PubInv/moonrat/RiceMiniCubator/CAD_MinicubatorTeam_Cycle5/CADRenderings_MinicubatorTeam_Cycle5.pdf

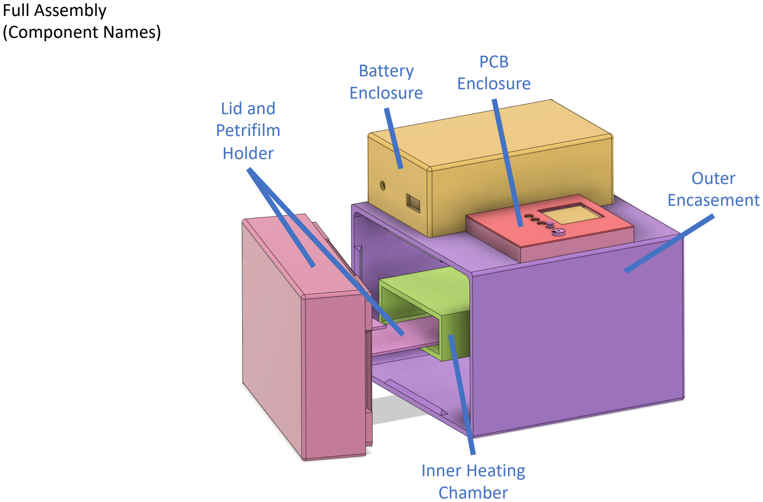
[picture p18: page 1]

Lid and
Petrifilm
Holder
Outer
Encasement

Inner Heating
Chamber

Battery
Enclosure

PCB
Enclosure

Full Assembly
(Component Names)

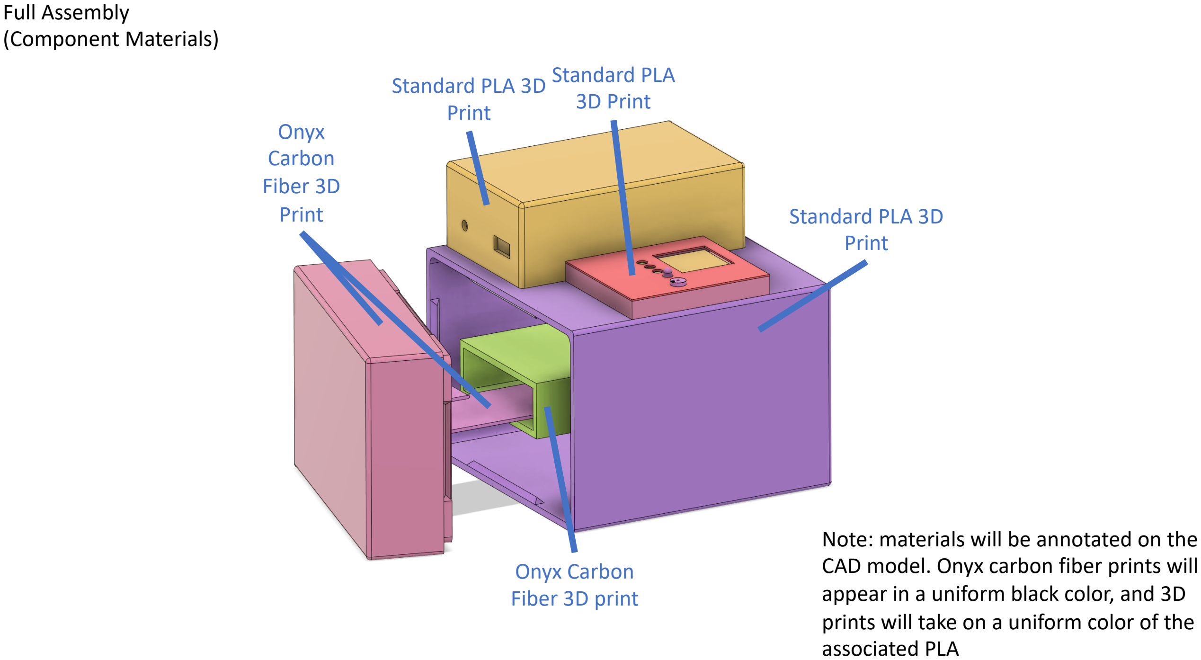
[picture p19: page 2]

Onyx
Carbon
Fiber 3D
Print | Standard PLA 3D
| Print

Onyx Carbon
Fiber 3D print

Standard PLA 3D
Print

Standard PLA
3D Print

Full Assembly
(Component Materials)

Note: materials will be annotated on the CAD model. Onyx carbon fiber prints will appear in a uniform black color, and 3D prints will take on a uniform color of the associated PLA

Inner Heating Chamber
(Material: Onyx Carbon Fiber) Note: this will be represented by a green box in future slides.

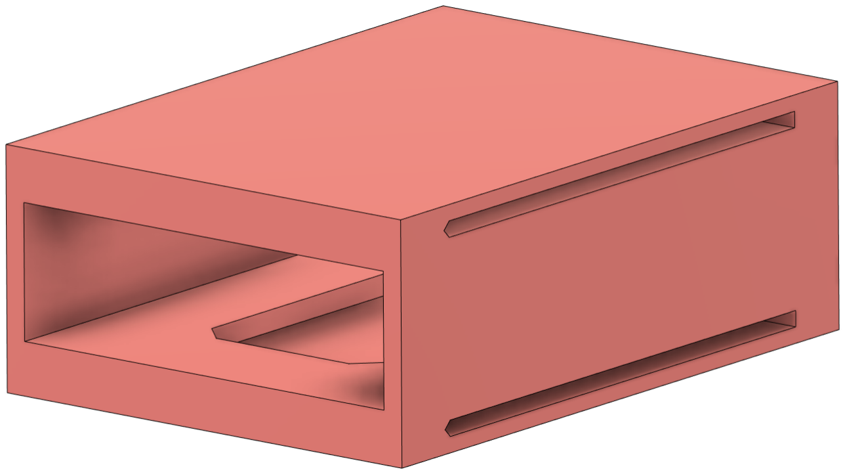
[picture p20: figure]

Inner Heating Chamber +
Outer Encasement, sans
Insulation (Materials
Shown)

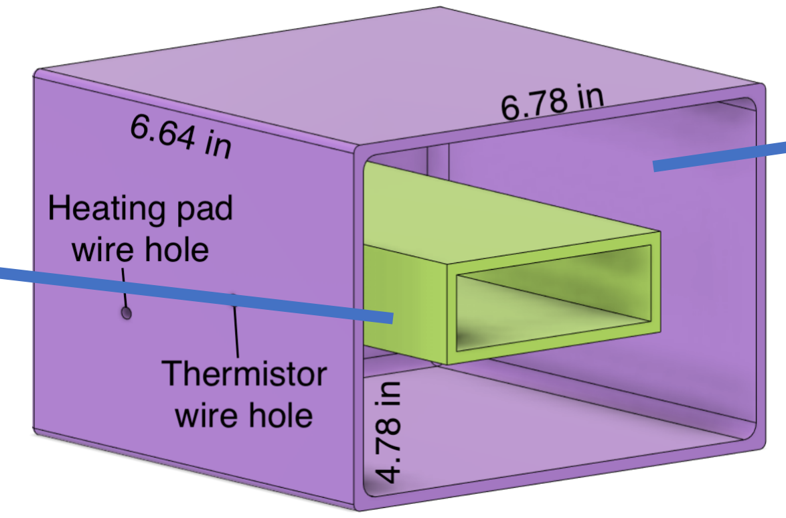
[picture p21: figure]

Onyx Carbon
Fiber

Standard PLA
3D Print

Note: the green inner heating chamber is a representation of the inner heating chamber on the previous slide. The inner dimensions with the petrifilm holder are left unchanged.

Placement of peg
mounting inner heating
chamber to the outer
enclosure

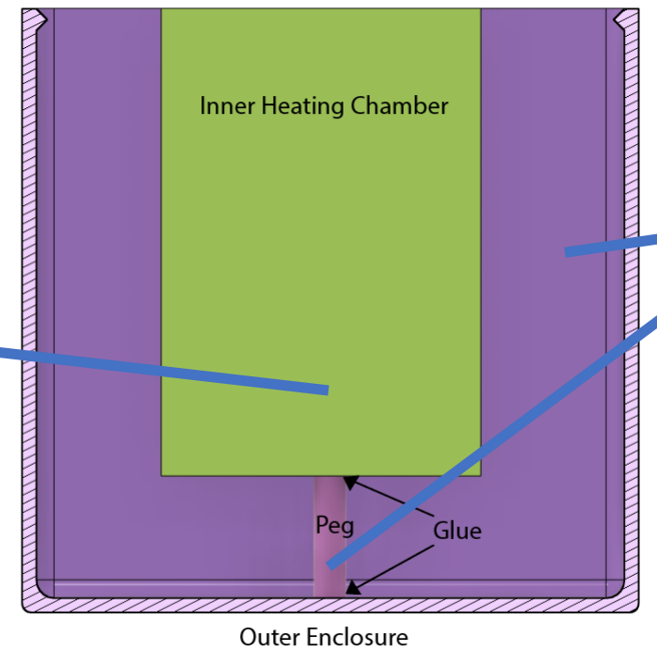
[picture p22: figure]

Onyx Carbon
Fiber

Standard PLA
3D Print

Inner Heating Chamber +
Insulation Material +
Outer Encasement
(Materials Shown)

Standard PLA
3D Print

Expanding

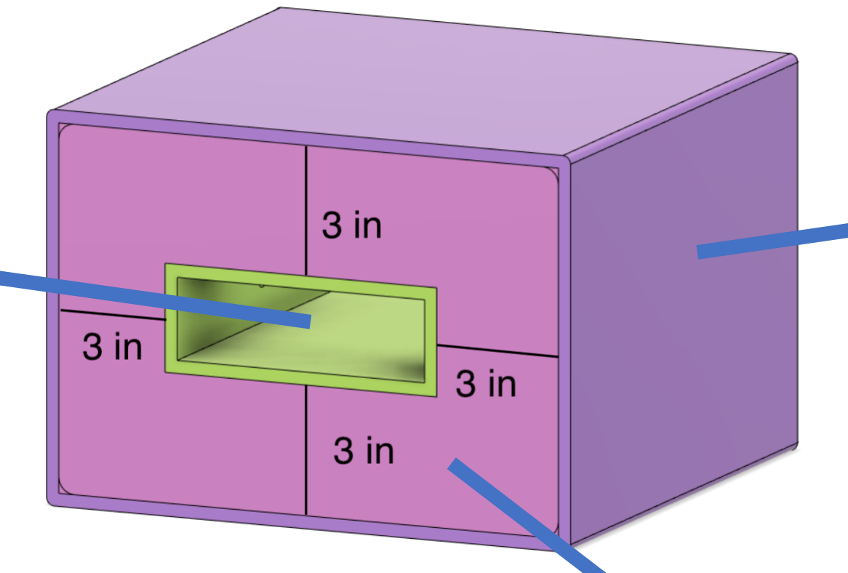
[picture p23: figure]

Polyurethane
Foam

Onyx Carbon
Fiber

Lid + Petrifilm Holder,
sans Insulation (Material: Onyx Carbon Fiber)

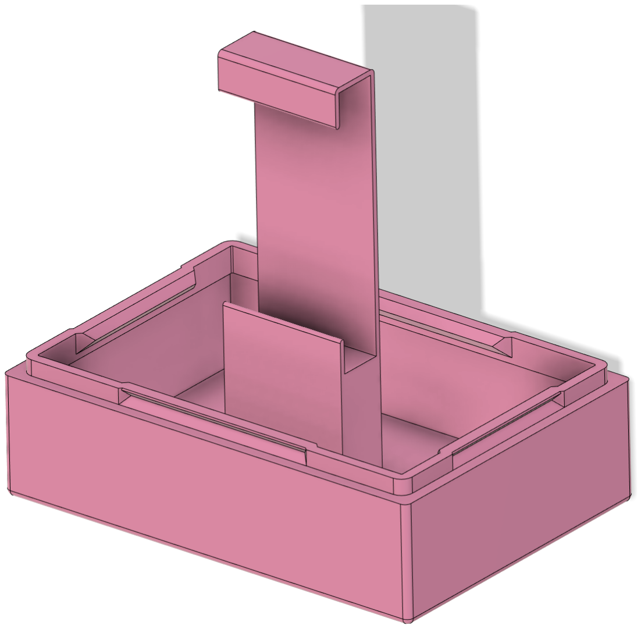
[picture p24: figure]

Lid + Petrifilm Holder,
interfaced with inner
heating chamber and
outer enclosure
(Materials Shown)

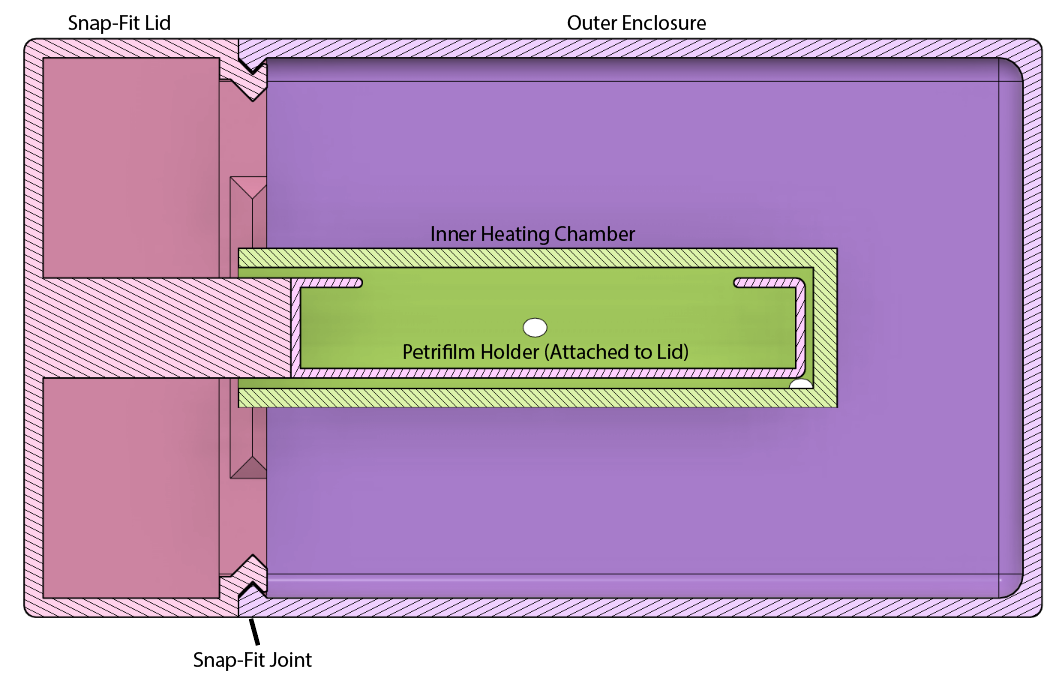
[picture p25: figure]

Onyx Carbon
Fiber
(Magenta,
Green)

PLA (purple)

Battery Enclosure and its mount on the outer encasement
(Material: PLA)

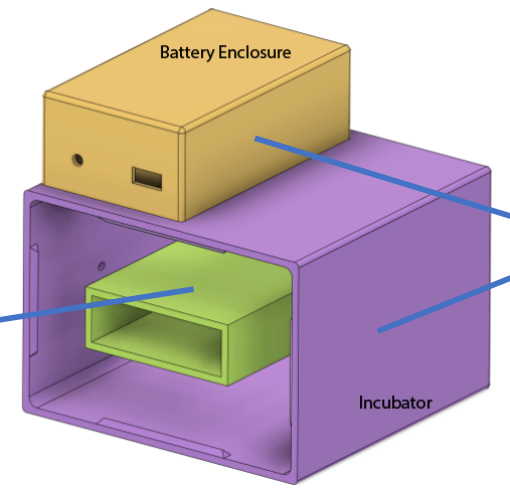
[picture p26: figure]

PLA

Onyx
Carbon
Fiber

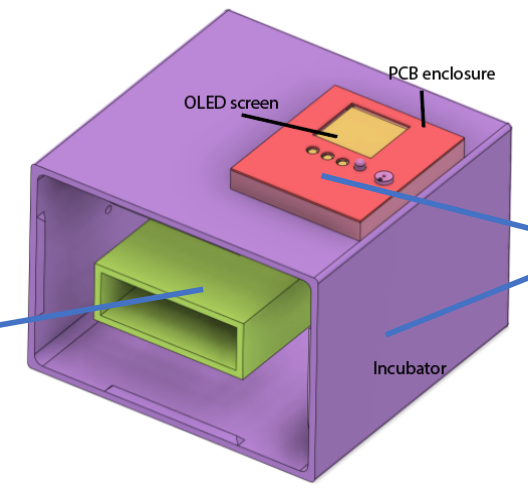
[picture p27: figure]

Onyx
Carbon
Fiber

PLA

PCB Enclosure and its mount on the outer encasement (Material: PLA)
