PubInv/moonrat/moonrat/ArduinoShieldIntermediate/ArduionShieldIntermediateDesign.jpg

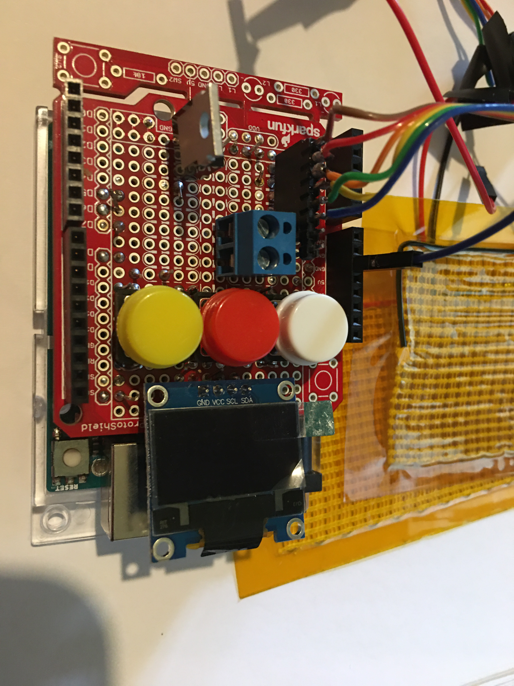
moonrat/ArduinoShieldIntermediate/ArduionShieldIntermediateDesign.jpg
