PubInv/moonrat/moonrat/PCB.gif

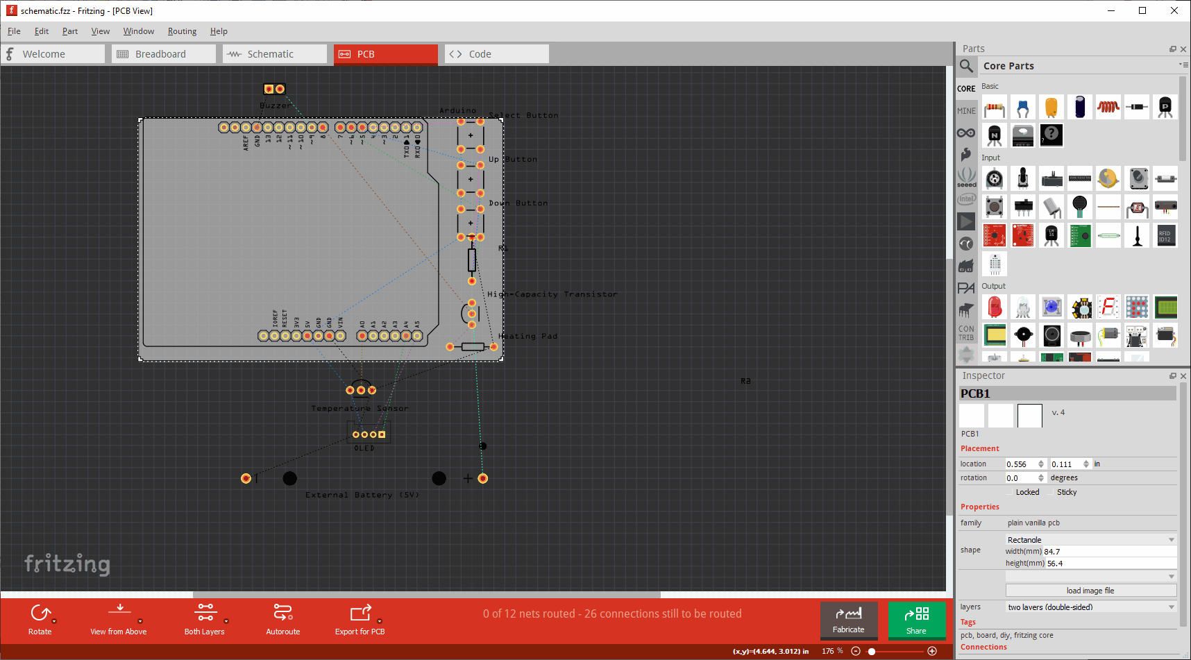
moonrat/PCB.gif
