PubInv/moonrat/moonrat/schematic.gif

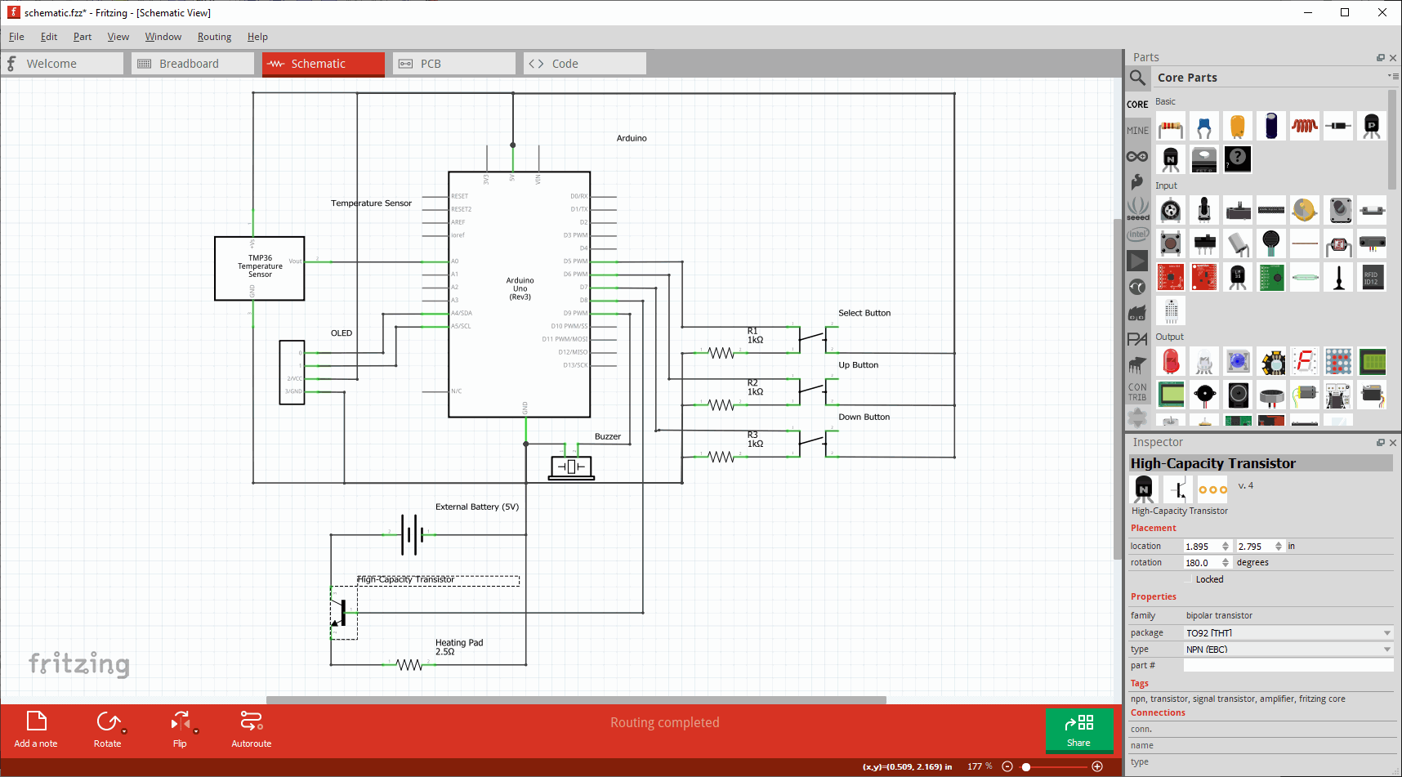
moonrat/schematic.gif
