PubInv/moonrat/moonrat/schematic.jpg

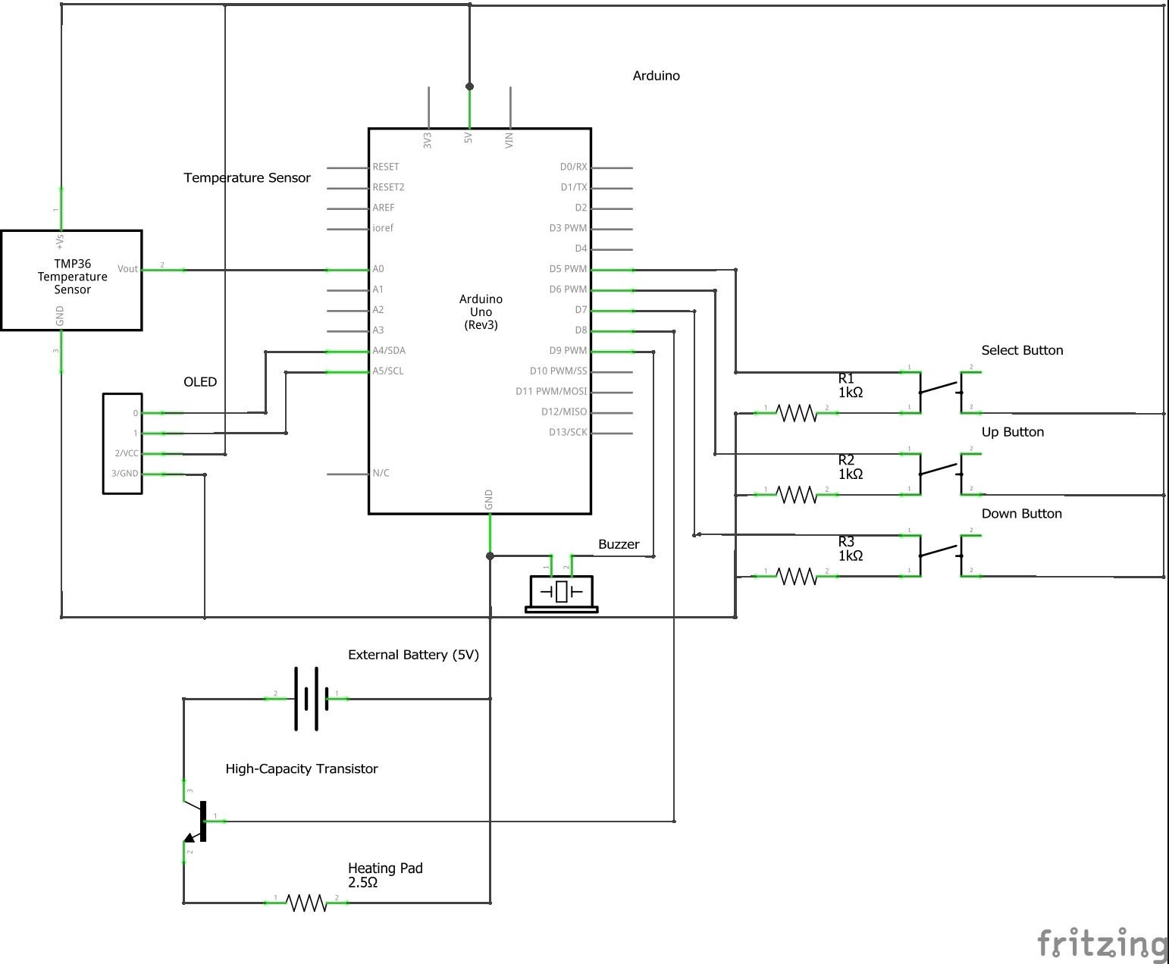
moonrat/schematic.jpg
