PubInv/moonrat/Pictures/IMG-2394.JPG

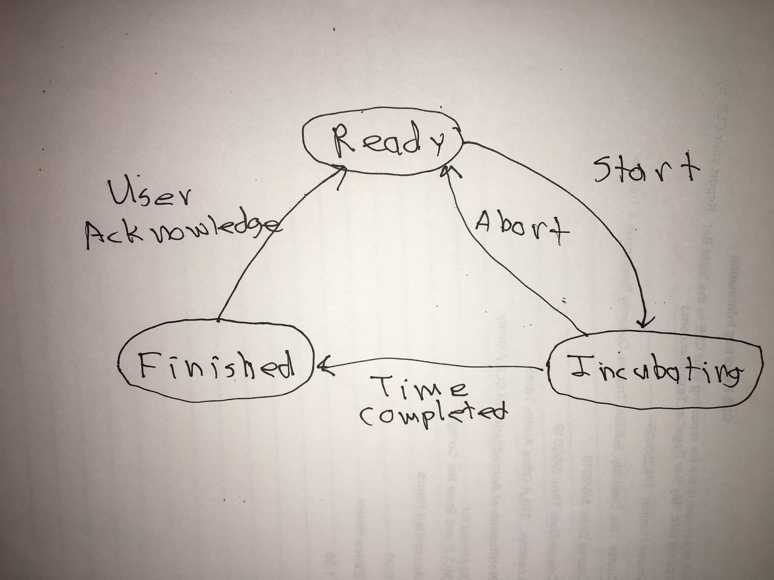
Pictures/IMG-2394.JPG
