PubInv/moonrat/Pictures/September2020/Full_Device.jpg

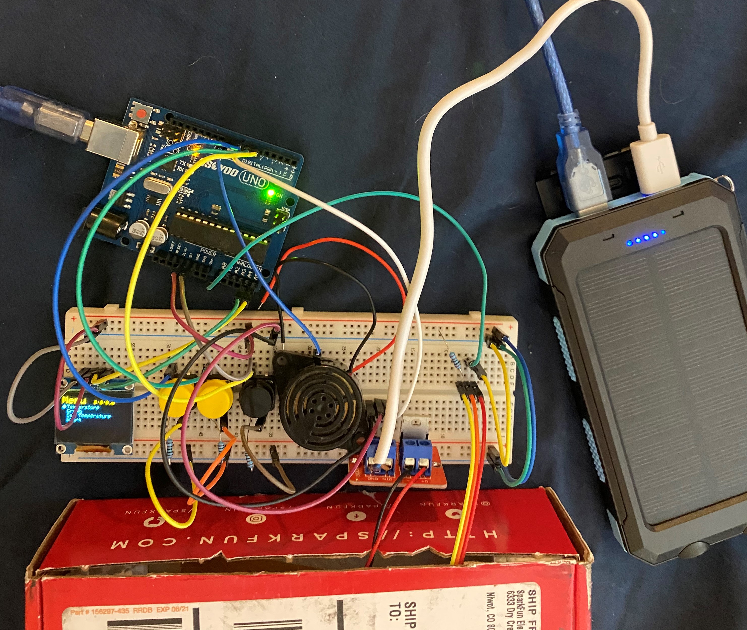
Pictures/September2020/Full_Device.jpg
