PubInv/moonrat/Pictures/September2020/Menu_Focus_2.jpg

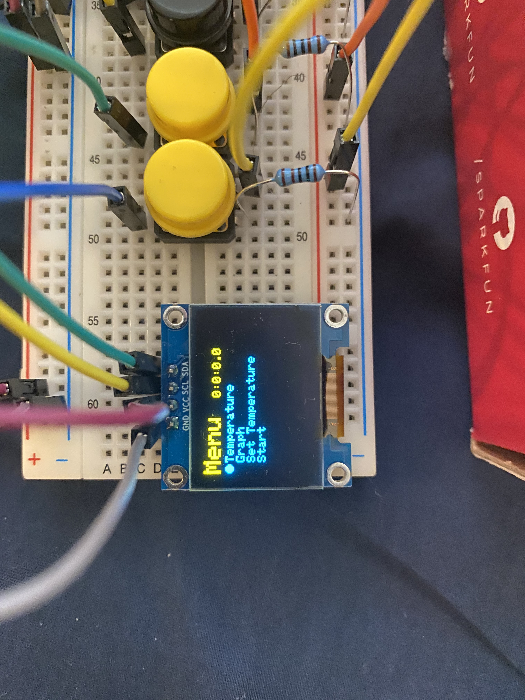
Pictures/September2020/Menu_Focus_2.jpg
