PubInv/moonrat/moonratII/hardware_moonratII/pcb_controller_moonratII/parts/Opossum_2978135/README.txt

Opossum by Amnson on Thingiverse: https://www.thingiverse.com/thing:2978135
