PubInv/moonrat/moonratII/hardware_moonratII/pcb_controller_moonratII/parts/Cable2x5.png

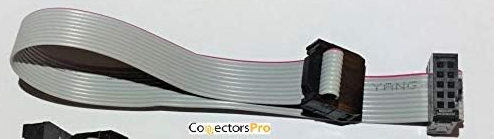
moonratII/hardware_moonratII/pcb_controller_moonratII/parts/Cable2x5.png
