PubInv/moonrat/moonratII/hardware_moonratII/pcb_controller_moonratII/parts/Cable_FemaleGND_2x3.png

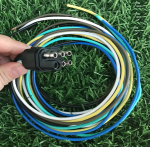
moonratII/hardware_moonratII/pcb_controller_moonratII/parts/Cable_FemaleGND_2x3.png
