PubInv/moonrat/moonratII/hardware_moonratII/pcb_controller_moonratII/parts/U602602_Dimension_New.jpg

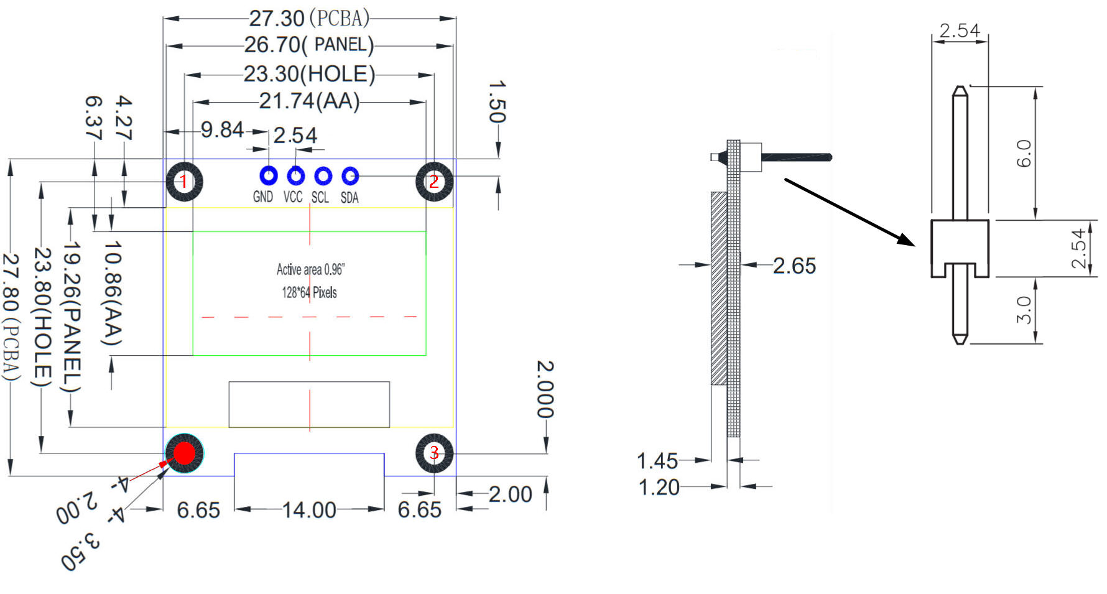
moonratII/hardware_moonratII/pcb_controller_moonratII/parts/U602602_Dimension_New.jpg
