PubInv/moonrat/moonratII/hardware_moonratII/pcb_controller_moonratII/parts/Omron/B3F-6050--3DModel-STEP-273799.STEP

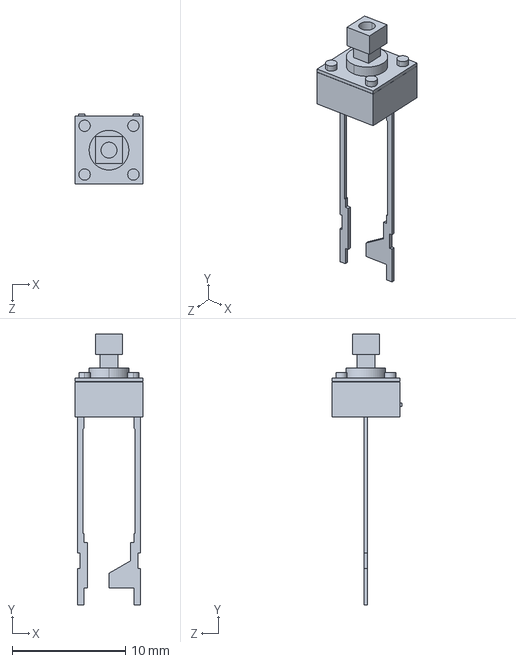
[picture p59: CAD file, 2023-07-31]
moonratII/hardware_moonratII/pcb_controller_moonratII/parts/Omron/B3F-6050--3DModel-STEP-273799.STEP
6.00 x 23.9 x 6.20 mm
