PubInv/moonrat/moonratII/hardware_moonratII/pcb_heaterboard_1_moonratII/parts/KF128 2.54mm/KF128-2.54-12P.step

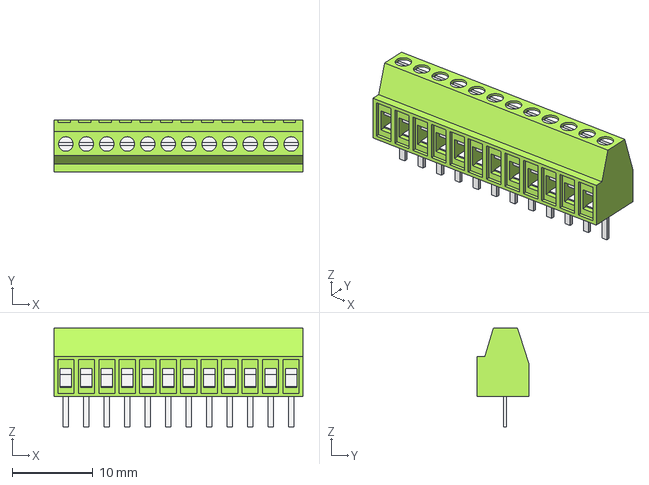
[picture p60: CAD file, 2025-05-26]
moonratII/hardware_moonratII/pcb_heaterboard_1_moonratII/parts/KF128 2.54mm/KF128-2.54-12P.step
30.9 x 6.50 x 12.3 mm
Housing
PlasticBody
