PubInv/moonrat/moonratII/hardware_moonratII/pcb_heaterboard_1_moonratII/parts/SMDRoundNut-PartBody_SMD_RoundNutM2x4x5x1.5.step

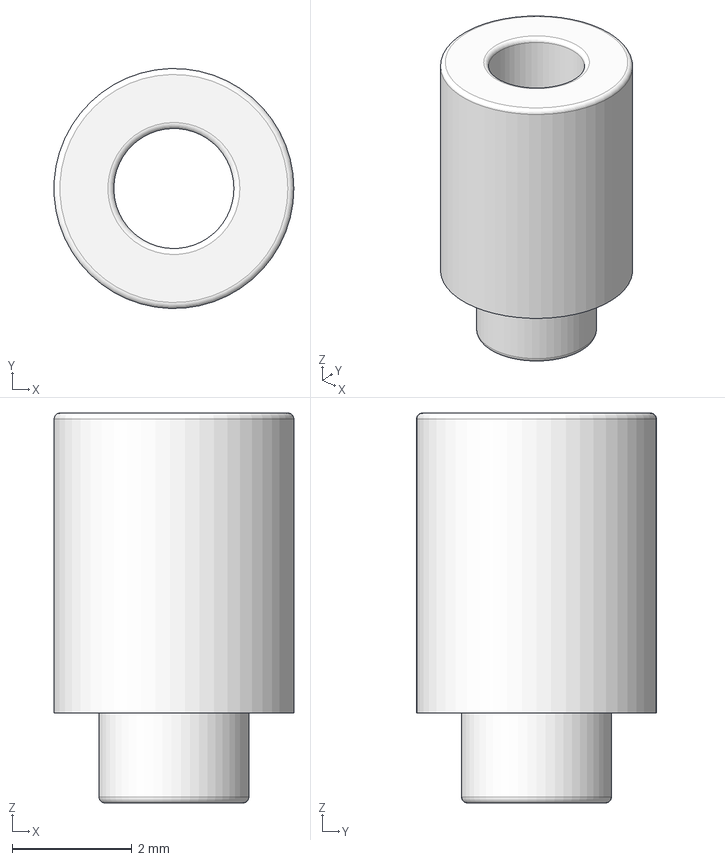
[picture p61: CAD file, 2023-11-20]
moonratII/hardware_moonratII/pcb_heaterboard_1_moonratII/parts/SMDRoundNut-PartBody_SMD_RoundNutM2x4x5x1.5.step
4.00 x 4.00 x 6.50 mm
