PubInv/moonrat/moonratII/hardware_moonratII/pcb_heaterboard_1_moonratII/parts/KF128 2.54mm/KF128-2.54-8P.step

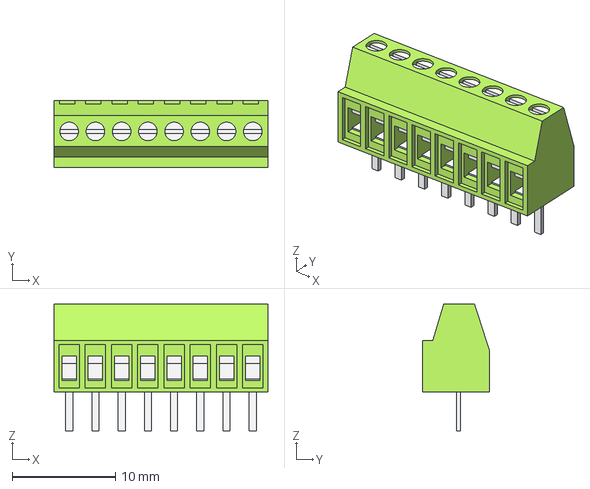
[picture p63: CAD file, 2025-05-26]
moonratII/hardware_moonratII/pcb_heaterboard_1_moonratII/parts/KF128 2.54mm/KF128-2.54-8P.step
20.7 x 6.50 x 12.3 mm
Housing
PlasticBody
