PubInv/moonrat/moonratII/hardware_moonratII/pcb_controller_moonratII/parts/homemade_2mmx3mmx3mmSpacer.FCStd

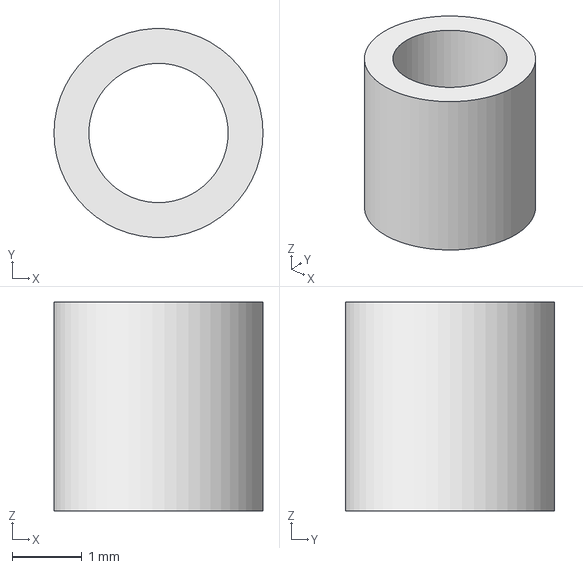
[picture p64: CAD file, 2023-11-19]
moonratII/hardware_moonratII/pcb_controller_moonratII/parts/homemade_2mmx3mmx3mmSpacer.FCStd
3.00 x 2.99 x 3.00 mm
