PubInv/moonrat/moonratII/hardware_moonratII/pcb_heaterboard_1_moonratII/parts/KF128 2.54mm/KF128-2.54-5P.step

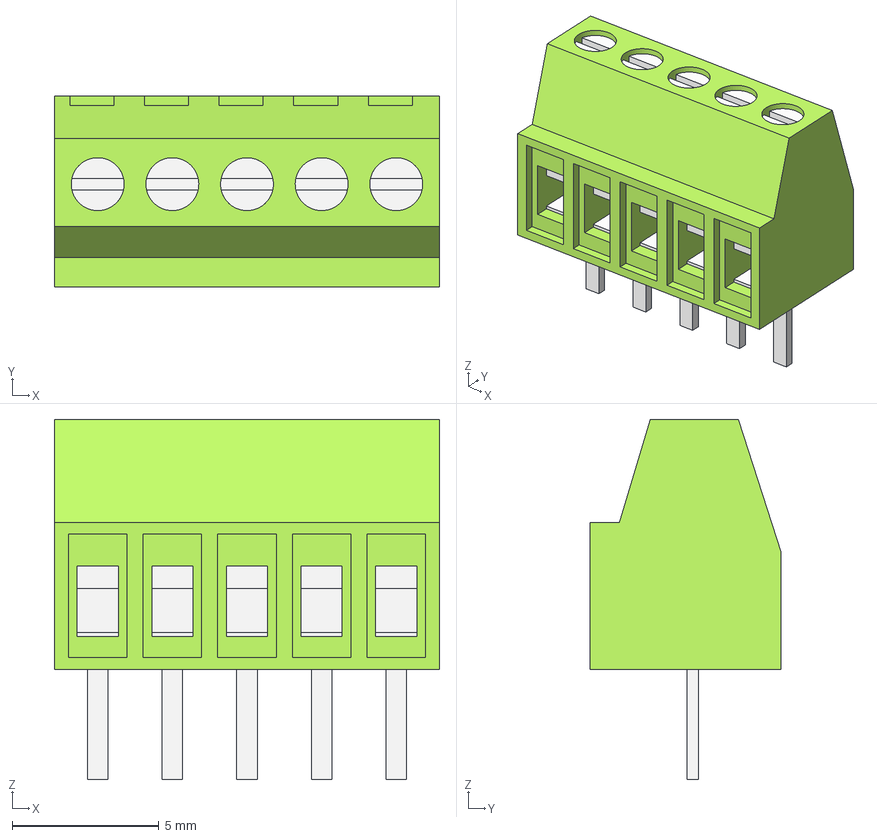
[picture p65: CAD file, 2025-05-26]
moonratII/hardware_moonratII/pcb_heaterboard_1_moonratII/parts/KF128 2.54mm/KF128-2.54-5P.step
13.1 x 6.50 x 12.3 mm
Housing
PlasticBody
