PubInv/moonrat/moonratII/hardware_moonratII/pcb_heaterboard_1_moonratII/parts/Pantalla OLED 0.96'' 128x64.stp

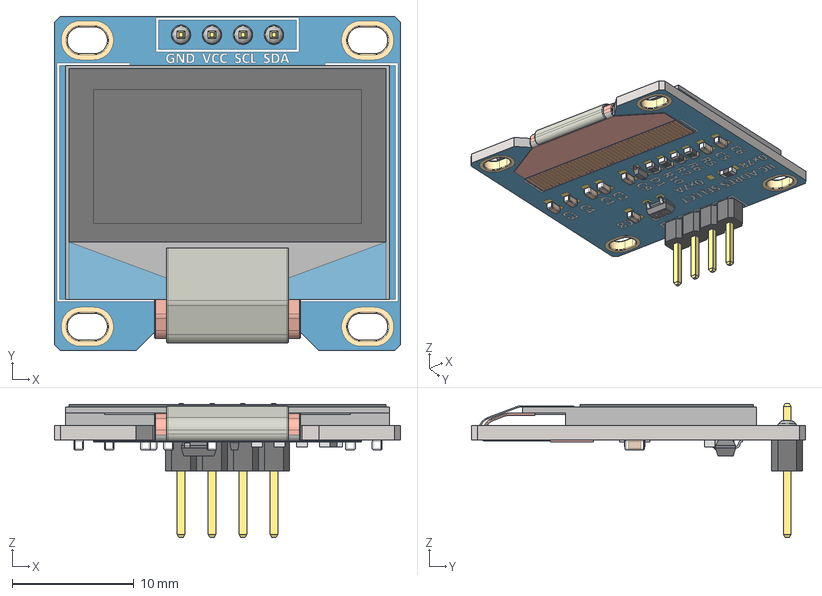
[picture p66: CAD file, 2023-11-19]
moonratII/hardware_moonratII/pcb_heaterboard_1_moonratII/parts/Pantalla OLED 0.96'' 128x64.stp
28.4 x 27.4 x 11.0 mm
SOT-23_TOR
RES_CR16_MTK_1 x 4
RES_CR16_MTK
SOD323F_DIO
