PubInv/moonrat/moonratII/hardware_moonratII/pcb_heaterboard_1_moonratII/parts/KF128 2.54mm/KF128-2.54-11P.step

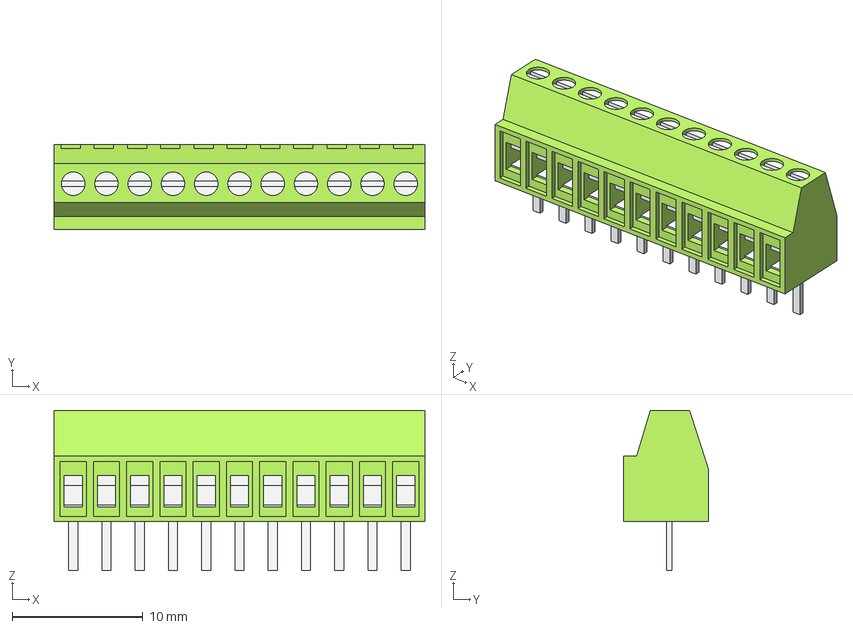
[picture p67: CAD file, 2025-05-26]
moonratII/hardware_moonratII/pcb_heaterboard_1_moonratII/parts/KF128 2.54mm/KF128-2.54-11P.step
28.3 x 6.50 x 12.3 mm
Housing
PlasticBody
