PubInv/moonrat/moonratII/hardware_moonratII/pcb_controller_moonratII/parts/SSD1306_OLED_Display(128x64).step

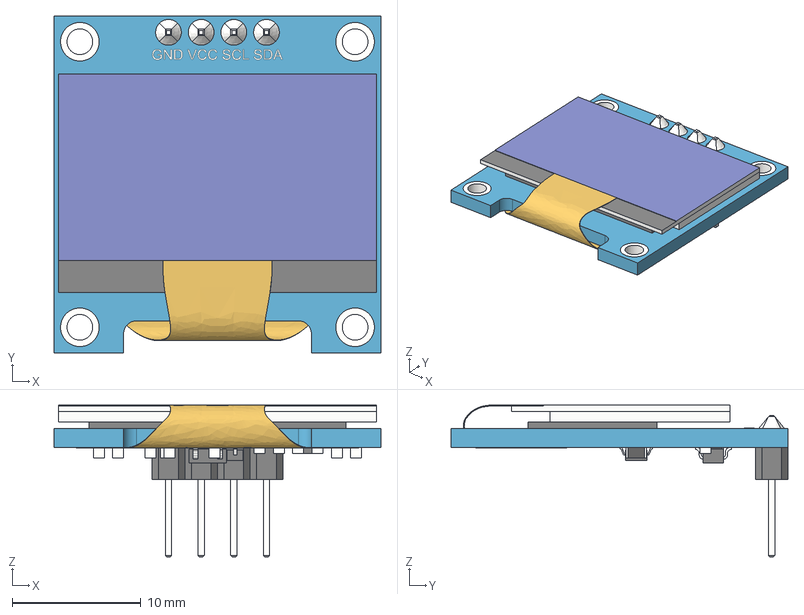
[picture p69: CAD file, 2023-08-16]
moonratII/hardware_moonratII/pcb_controller_moonratII/parts/SSD1306_OLED_Display(128x64).step
25.4 x 26.2 x 11.8 mm
board
screen
pin_header
soldering
smd_capacitor
smd_capacitor (1)
914_smd_resistor
472_smd_resistor x 3
t4_smd_diode
smd_capacitor (2)
smd_capacitor (3)
smd_capacitor (4)
smd_capacitor (5)
smd_capacitor (6)
472_smd_resistor (1)
SOT-23_XC6206 v3
smd_capacitor (7)
flat_cable
