PubInv/moonrat/moonratII/hardware_moonratII/pcb_controller_moonratII/parts/BarrelJackSMD v3.step

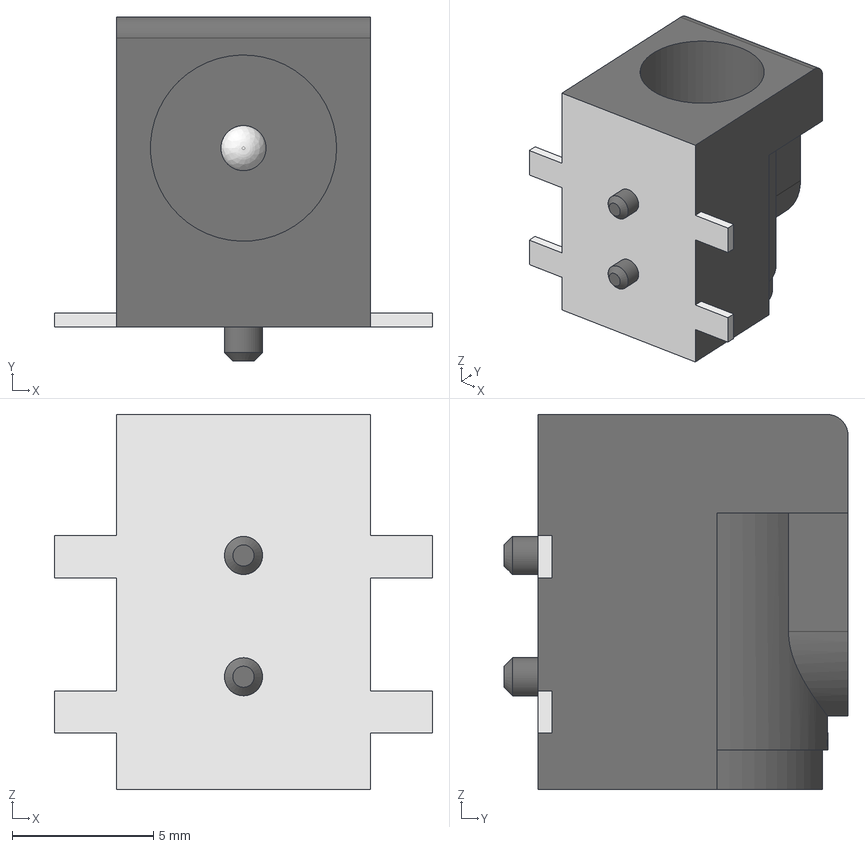
[picture p71: CAD file, 2023-08-03]
moonratII/hardware_moonratII/pcb_controller_moonratII/parts/BarrelJackSMD v3.step
13.4 x 12.2 x 13.3 mm
