PubInv/moonrat/moonratII/hardware_moonratII/pcb_heaterboard_1_moonratII/manufacturing_test/Assembly_photos_Rev1/20240217_200506.jpg

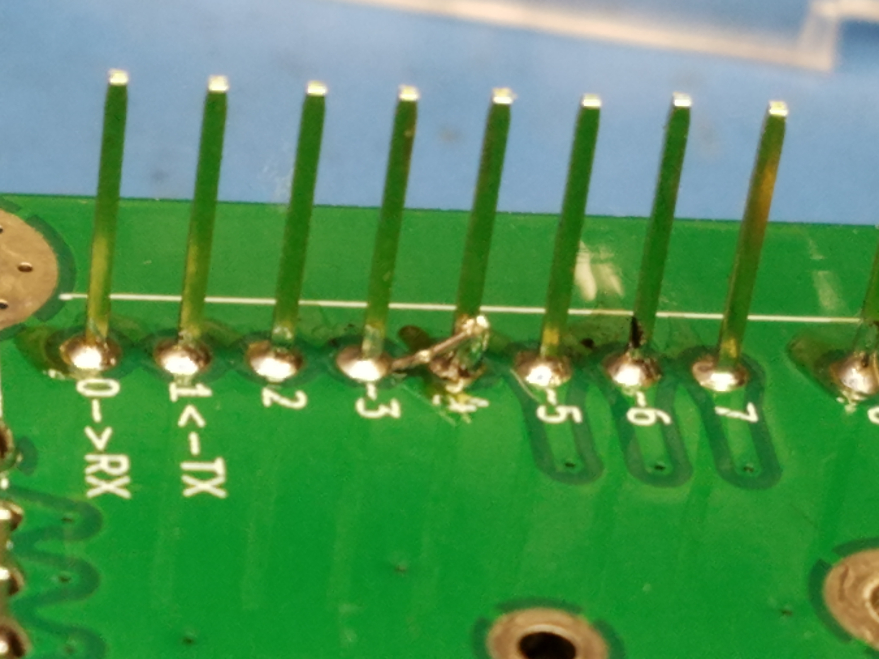
moonratII/hardware_moonratII/pcb_heaterboard_1_moonratII/manufacturing_test/Assembly_photos_Rev1/20240217_200506.jpg
