PubInv/moonrat/moonratII/testing_moonratII/heat_map_moonratII/3d_view.png

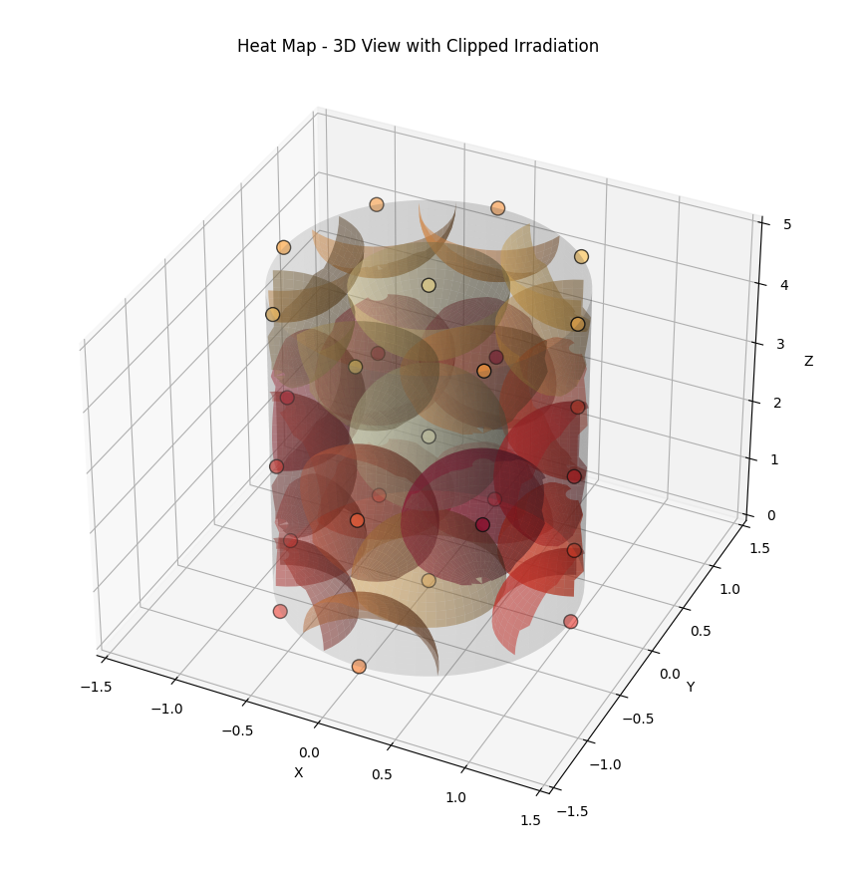
moonratII/testing_moonratII/heat_map_moonratII/3d_view.png
