PubInv/moonrat/moonratII/testing_moonratII/heat_map_moonratII/lat_view.png

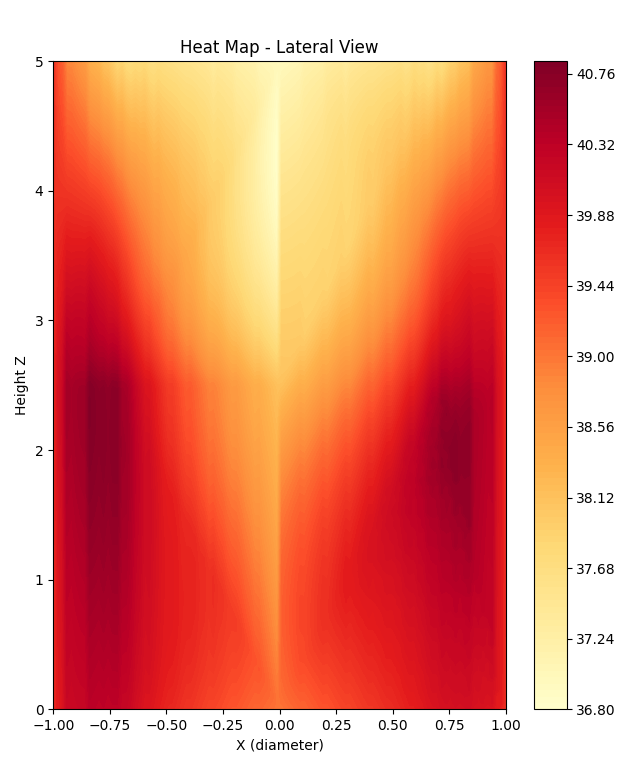
moonratII/testing_moonratII/heat_map_moonratII/lat_view.png
