PubInv/moonrat/moonratII/testing_moonratII/heat_map_moonratII/top_view.png

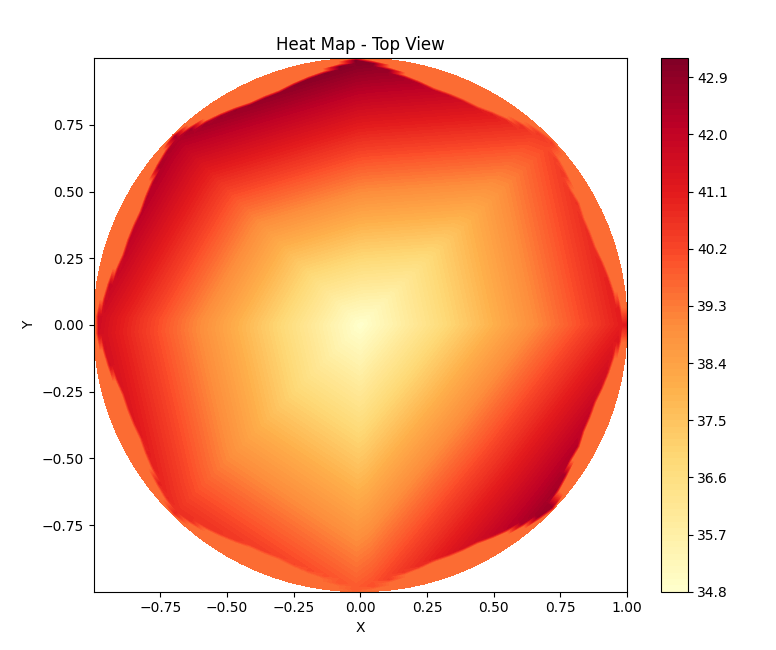
moonratII/testing_moonratII/heat_map_moonratII/top_view.png
