PubInv/moonrat/moonratII/hardware_moonratII/pcb_controller_moonratII/parts/C5665.pdf

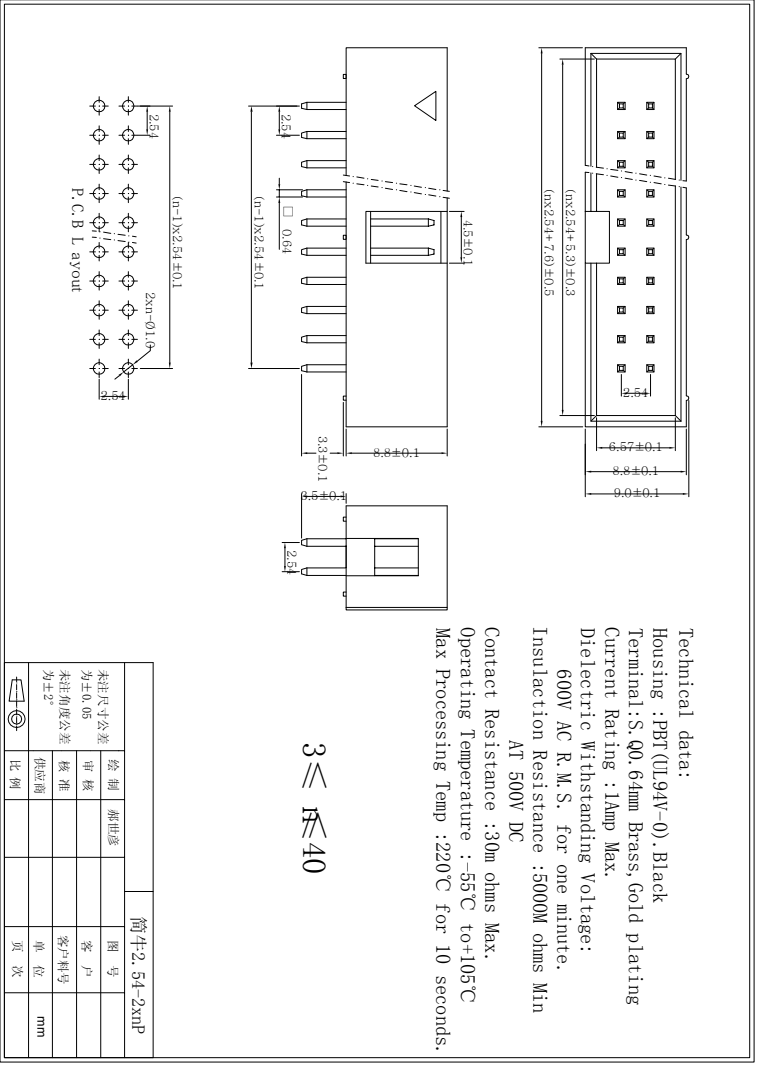
[picture p118: page 1]
P.C.B L ayout; Technical data:; 简牛2.54-2xnP; 未注角度公差; 未注尺寸公差; 供应商; 客户料号; 郝世彦

Max Processing Temp :220℃ for 10 seconds.

Operating Temperature :-55℃ to+105℃

Contact Resistance :30m ohms Max.

Insulaction Resistance :5000M ohms Min

Dielectric Withstanding Voltage:

Current Rating :1Amp Max.

Terminal:S.Q0.64mm Brass,Gold plating

Housing :PBT(UL94V-0).Black

600V AC R.M.S. for one minute.
