PubInv/moonrat/moonratII/hardware_moonratII/pcb_controller_moonratII/parts/DB128V-5.08-2P-GN-S.pdf

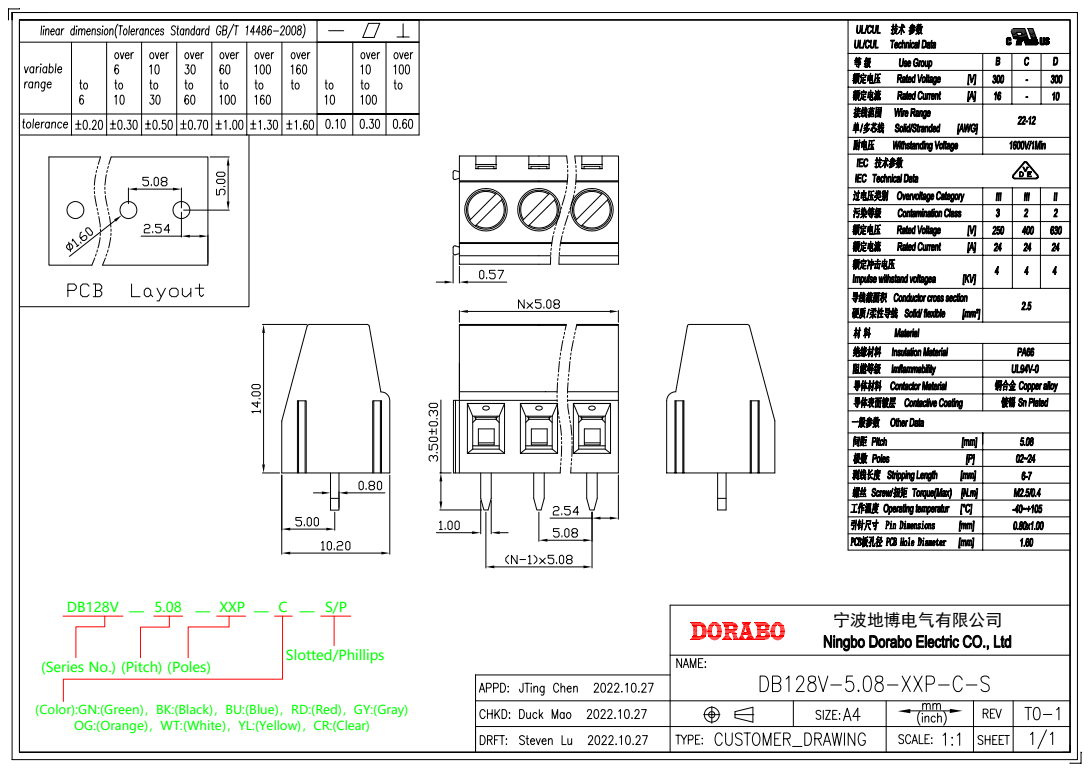
[picture p119: page 1]
— XXP; — S/P (Series No.) (Pitch) (Poles); Slotted/Phillips; 宁波地博电气有限公司 (Color):GN:(Green)，BK:(Black)，BU:(Blue)，RD:(Red)，GY:(Gray) OG:(Orange)，WT:(White)，YL:(Yellow)，CR:(Clear)
