PubInv/moonrat/RiceMiniCubator/MicrocontrollerCode_MinicubatorTeam_Cycle5.pdf

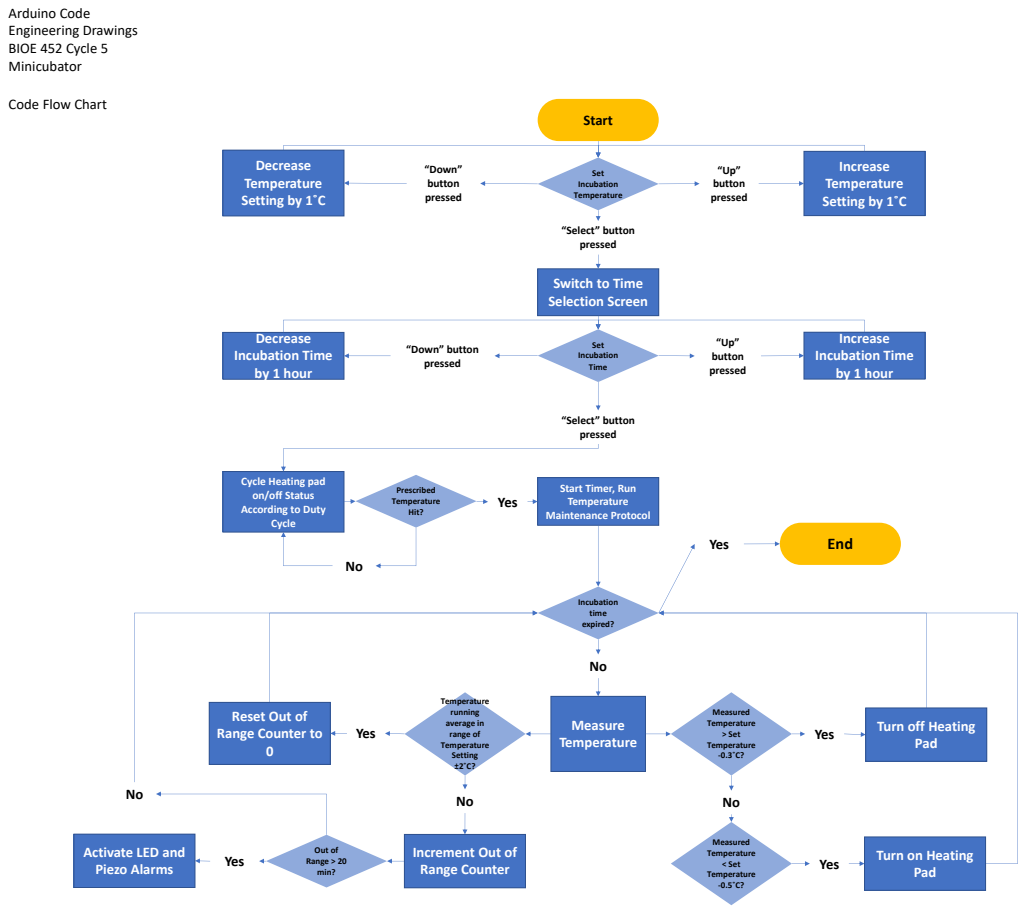
[picture p120: page 1]
Arduino Code Engineering Drawings BIOE 452 Cycle 5 Minicubator; Start; Set Incubation Temperature; Decrease Temperature Setting by 1˚C; Increase Temperature Setting by 1˚C; Set Incubation Time; Decrease Incubation Time by 1 hour; Increase Incubation Time by 1 hour; “Down” button pressed; “Up” button pressed; “Select” button pressed; Incubation time expired?; End; Measured Temperature > Set Temperature -0.3˚C?; Measured Temperature < Set Temperature -0.5˚C?; Yes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

Code Flow Chart

Switch to Time
Selection Screen

Cycle Heating pad
on/off Status
According to Duty
Cycle

Start Timer, Run
Temperature
Maintenance Protocol

Reset Out of
Range Counter to

Turn off Heating
Pad

Activate LED and
Piezo Alarms

Increment Out of
Range Counter

Turn on Heating

## User Control

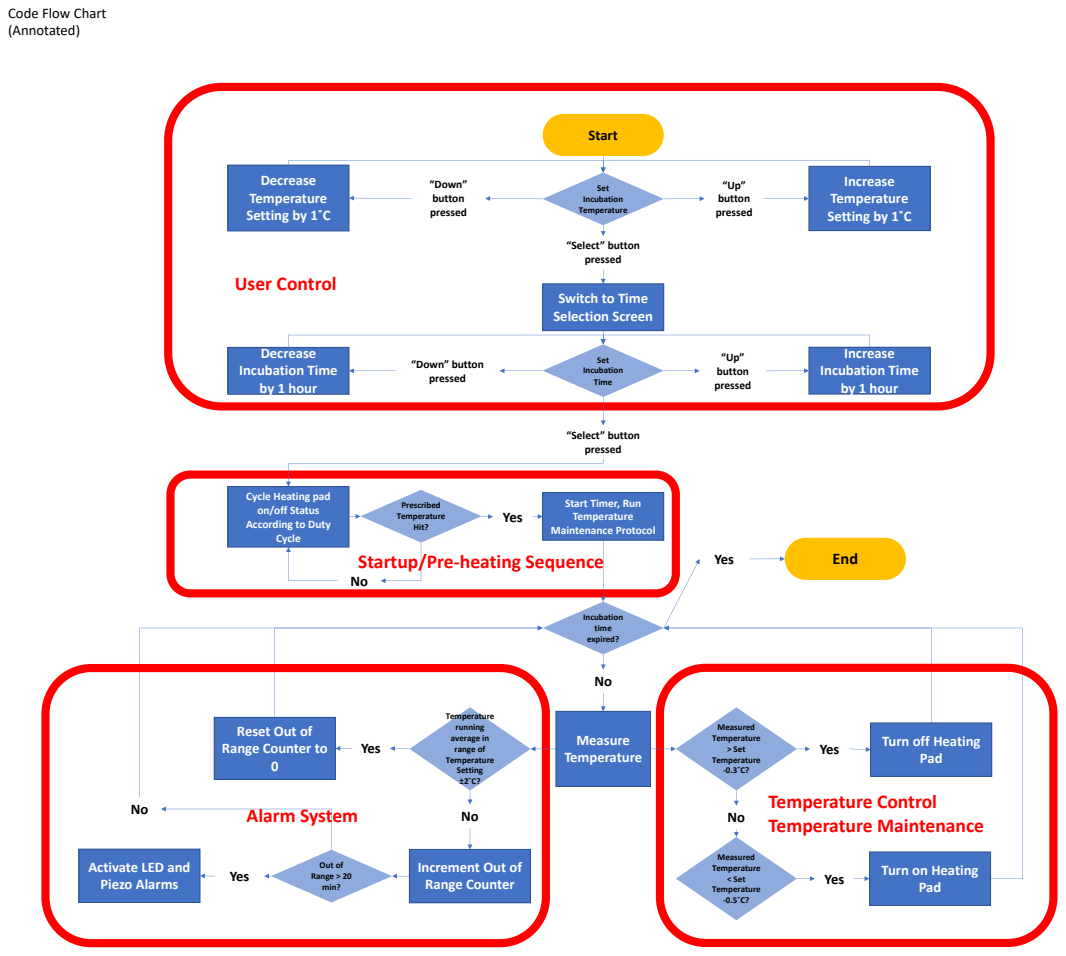
[picture p121: page 2]
Start; Set Incubation Temperature; Decrease Temperature Setting by 1˚C; Increase Temperature Setting by 1˚C; Set Incubation Time; Decrease Incubation Time by 1 hour; Increase Incubation Time by 1 hour; “Down” button pressed; “Up” button pressed; “Select” button pressed; Incubation time expired?; End; Measured Temperature > Set Temperature -0.3˚C?; Measured Temperature < Set Temperature -0.5˚C?; Yes; Temperature running average in range of Temperature Setting ±2˚C?; Out of Range > 20 min?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

Code Flow Chart
(Annotated)

Switch to Time
Selection Screen

Cycle Heating pad
on/off Status
According to Duty
Cycle

Start Timer, Run
Temperature
Maintenance Protocol

Reset Out of
Range Counter to

Turn off Heating
Pad

Activate LED and
Piezo Alarms

Increment Out of
Range Counter

Turn on Heating
