PubInv/moonrat/RiceMiniCubator/CAD_MinicubatorTeam_Cycle5/InnerHeatingChamber_MinicubatorTeam_Cycle5.pdf

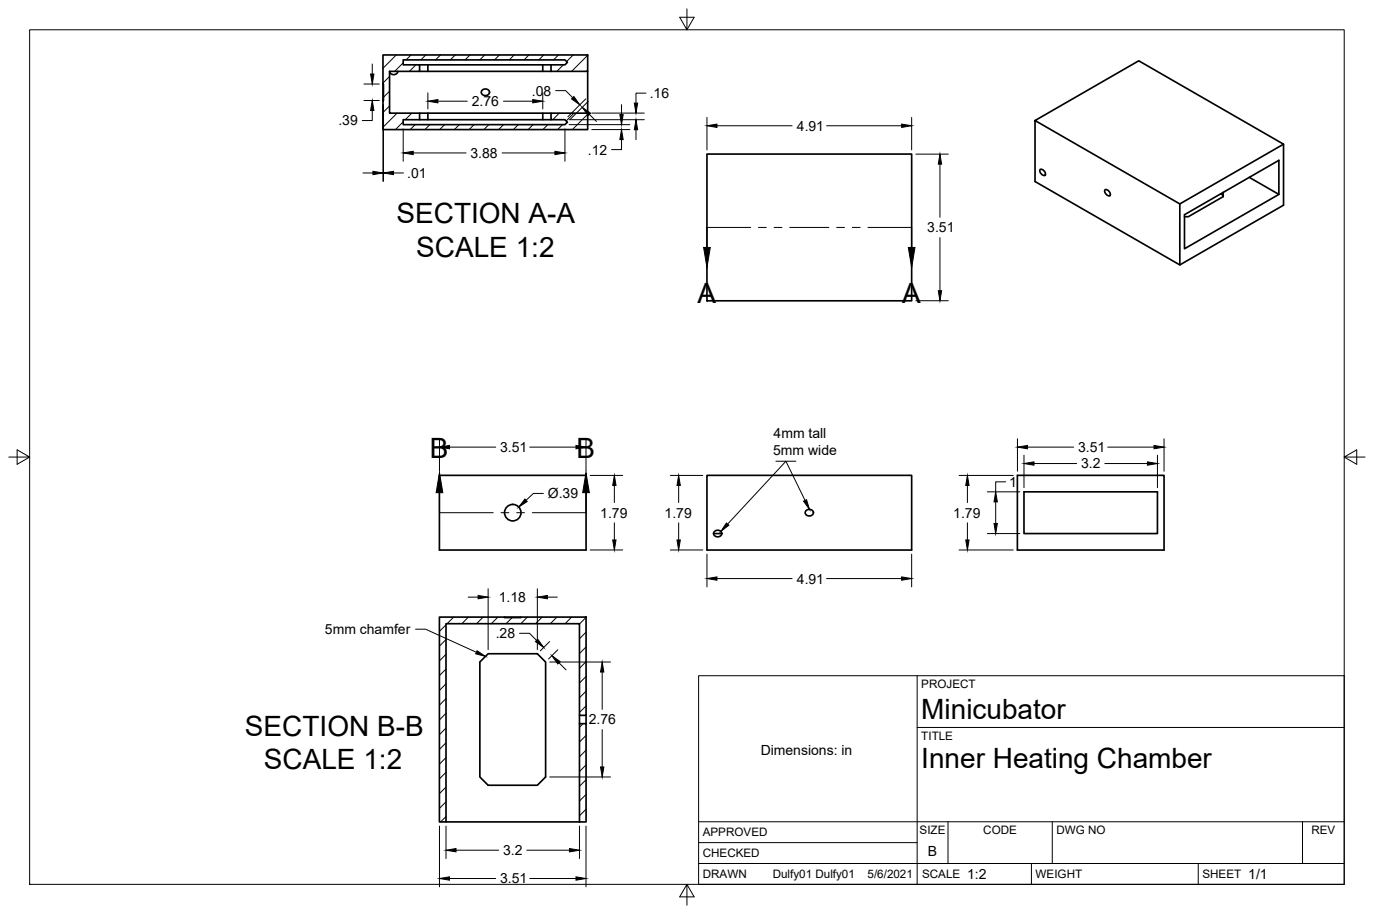
[picture p122: page 1]
SIZE; CODE; DWG NO; REV; Dulfy01 Dulfy01 5/6/2021; 4mm tall 5mm wide; SECTION A-A SCALE 1:2; SECTION B-B SCALE 1:2; .28 5mm chamfer; Dimensions: in

PROJECT
Minicubator
Inner Heating Chamber
