PubInv/moonrat/RiceMiniCubator/CAD_MinicubatorTeam_Cycle5/LidPetrifilmHolder_MinicubatorTeam_Cycle4.pdf

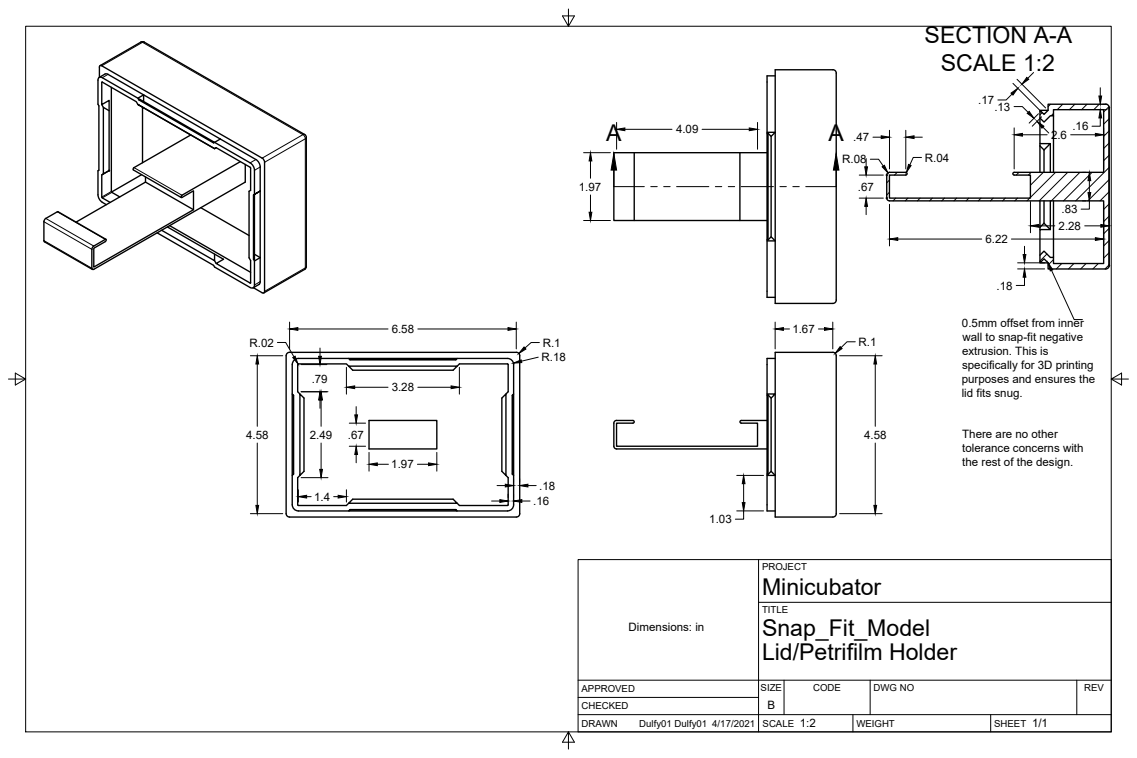
[picture p123: page 1]
SIZE; CODE; DWG NO; REV; Dulfy01 Dulfy01 4/17/2021; Lid/Petrifilm Holder; SECTION A-A SCALE 1:2; Dimensions: in

0.5mm offset from inner
wall to snap-fit negative
extrusion. This is
specifically for 3D printing
purposes and ensures the
lid fits snug.

There are no other
tolerance concerns with
the rest of the design.
