PubInv/moonrat/RiceMiniCubator/CAD_MinicubatorTeam_Cycle5/OuterEncasement_MinicubatorTeam_Cycle4.pdf

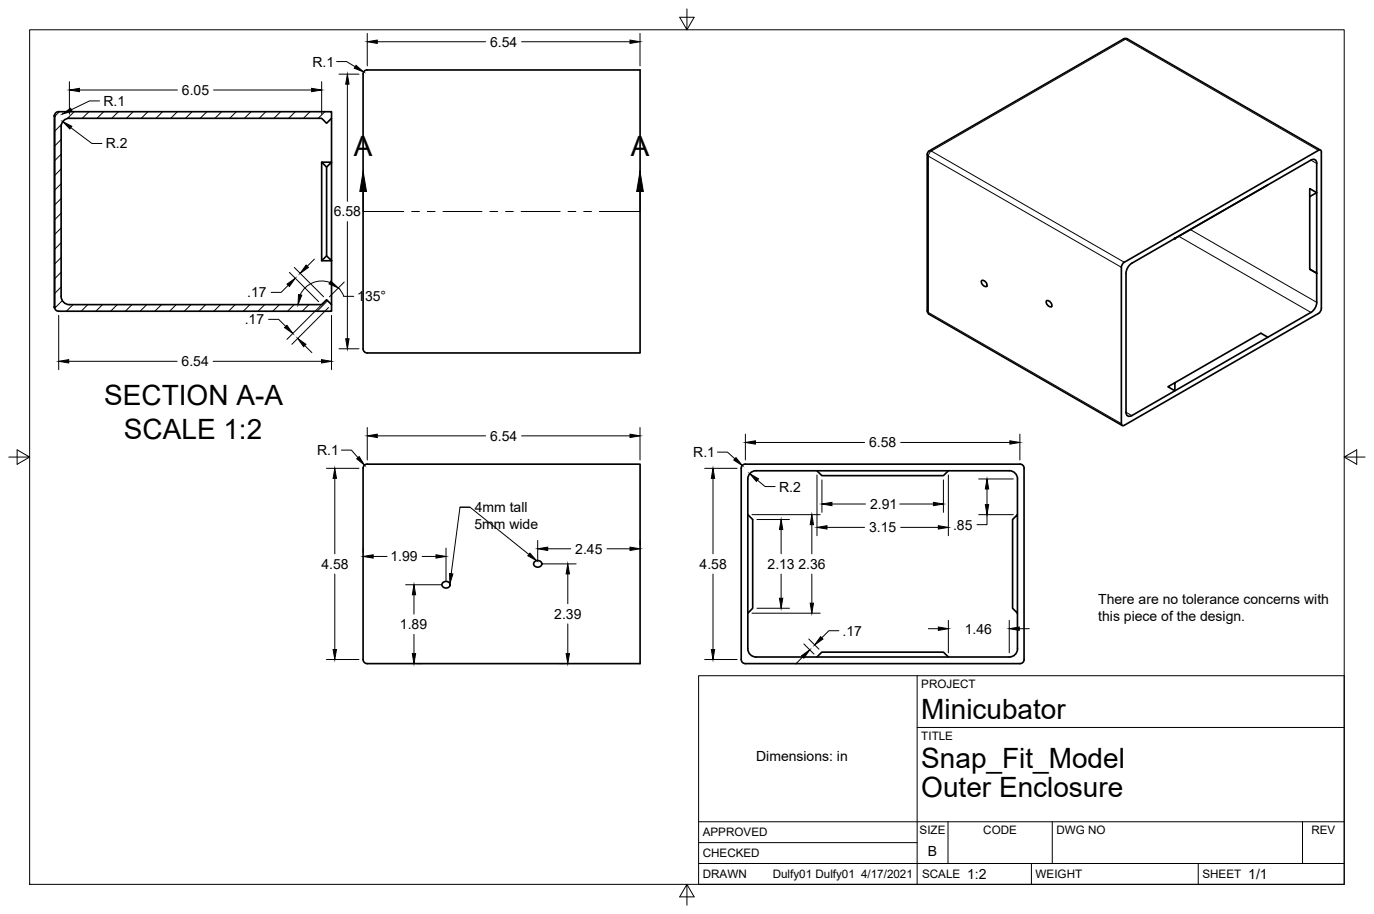
[picture p124: page 1]
SIZE; CODE; DWG NO; REV; Dulfy01 Dulfy01 4/17/2021; Outer Enclosure; SECTION A-A SCALE 1:2; 4mm tall 5mm wide; Dimensions: in

There are no tolerance concerns with
this piece of the design.
