PubInv/moonrat/RiceMiniCubator/CAD_MinicubatorTeam_Cycle5/BatteryEnclosure_MinicubatorTeam_Cycle4.pdf

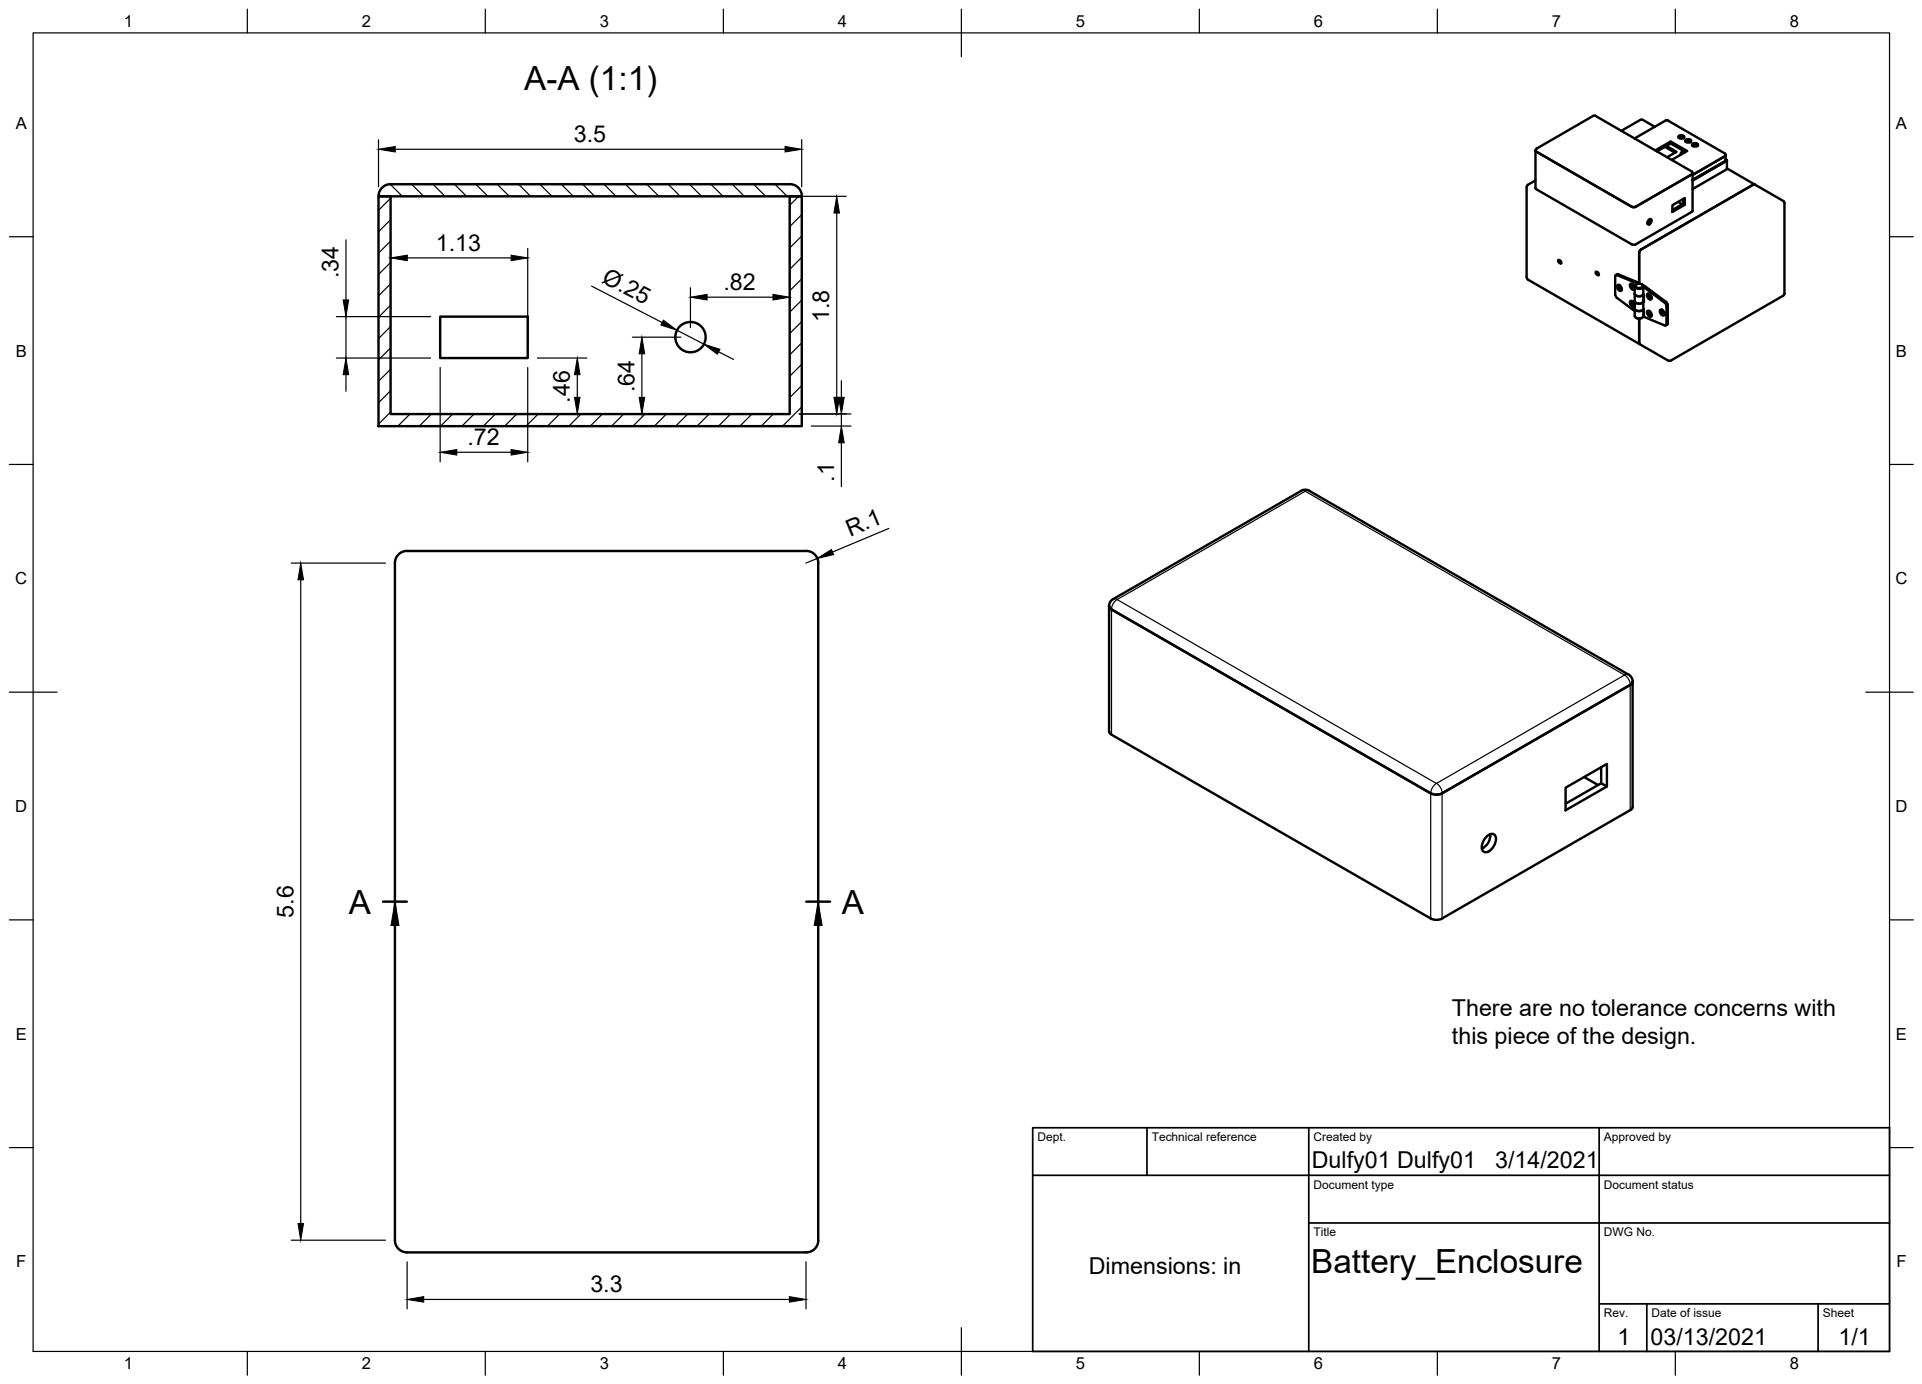
[picture p125: page 1]
Title; DWG No.; Rev.; Date of issue; Sheet; Dimensions: in .64

There are no tolerance concerns with
this piece of the design.

Dept. | Technical reference | Created by Dulfy01 Dulfy01 3/14/2021 | Approved by

Document type | Document status
