PubInv/moonrat/Pictures/September2020/Menu_Focus.jpg

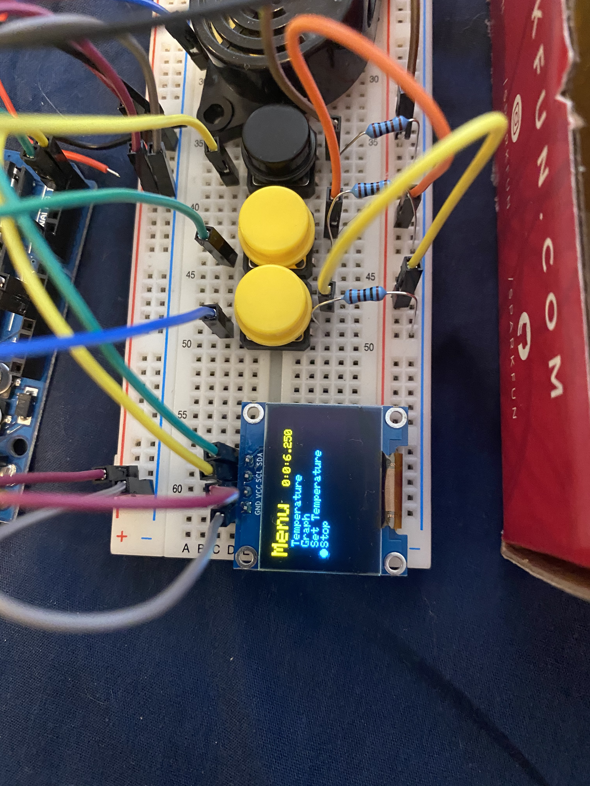
Pictures/September2020/Menu_Focus.jpg
