PubInv/moonrat/Pictures/September2020/Temperature_Reading.jpg

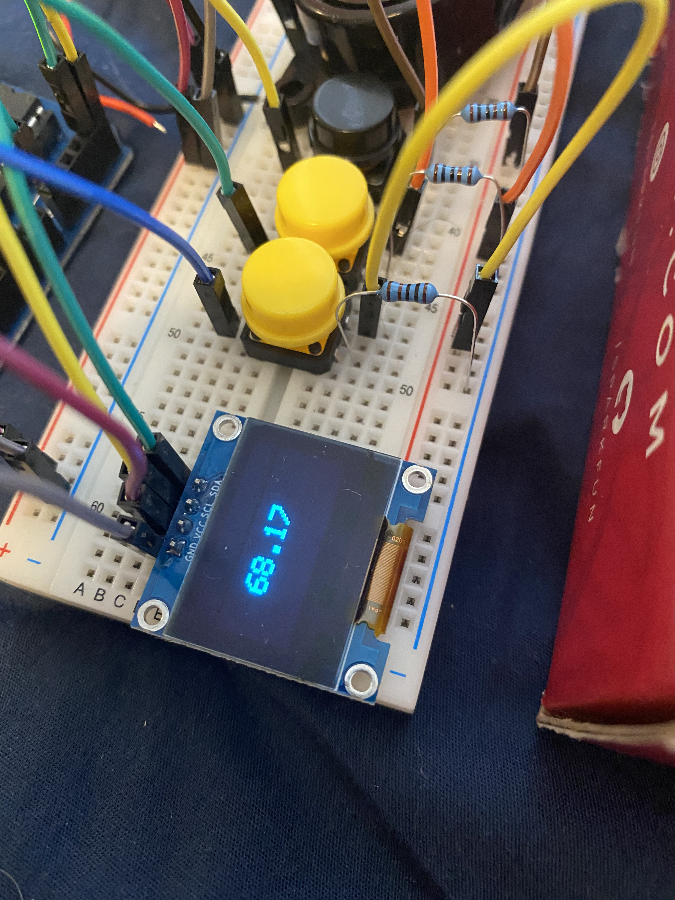
Pictures/September2020/Temperature_Reading.jpg
